Stachu1/STM32_Watch/firmware/types.h

#ifndef _TYPES_H
#define _TYPES_H

#include <stdint.h>
#include <stddef.h>

typedef uint8_t   u8;
typedef uint16_t u16;
typedef uint32_t u32;
typedef uint64_t u64;

typedef int8_t   i8;
typedef int16_t i16;
typedef int32_t i32;
typedef int64_t i64;

typedef u8   b8;
typedef u16 b16;
typedef u32 b32;
typedef u64 b64;

typedef char c;

#ifndef true
#define true 1
#define false 0
#endif

#endif
